hopper775/Analog_t12_controller/t12 iron/t12 iron.kicad_pcb

## KiCad design v0.0.1/cwbpf.kicad_pcb

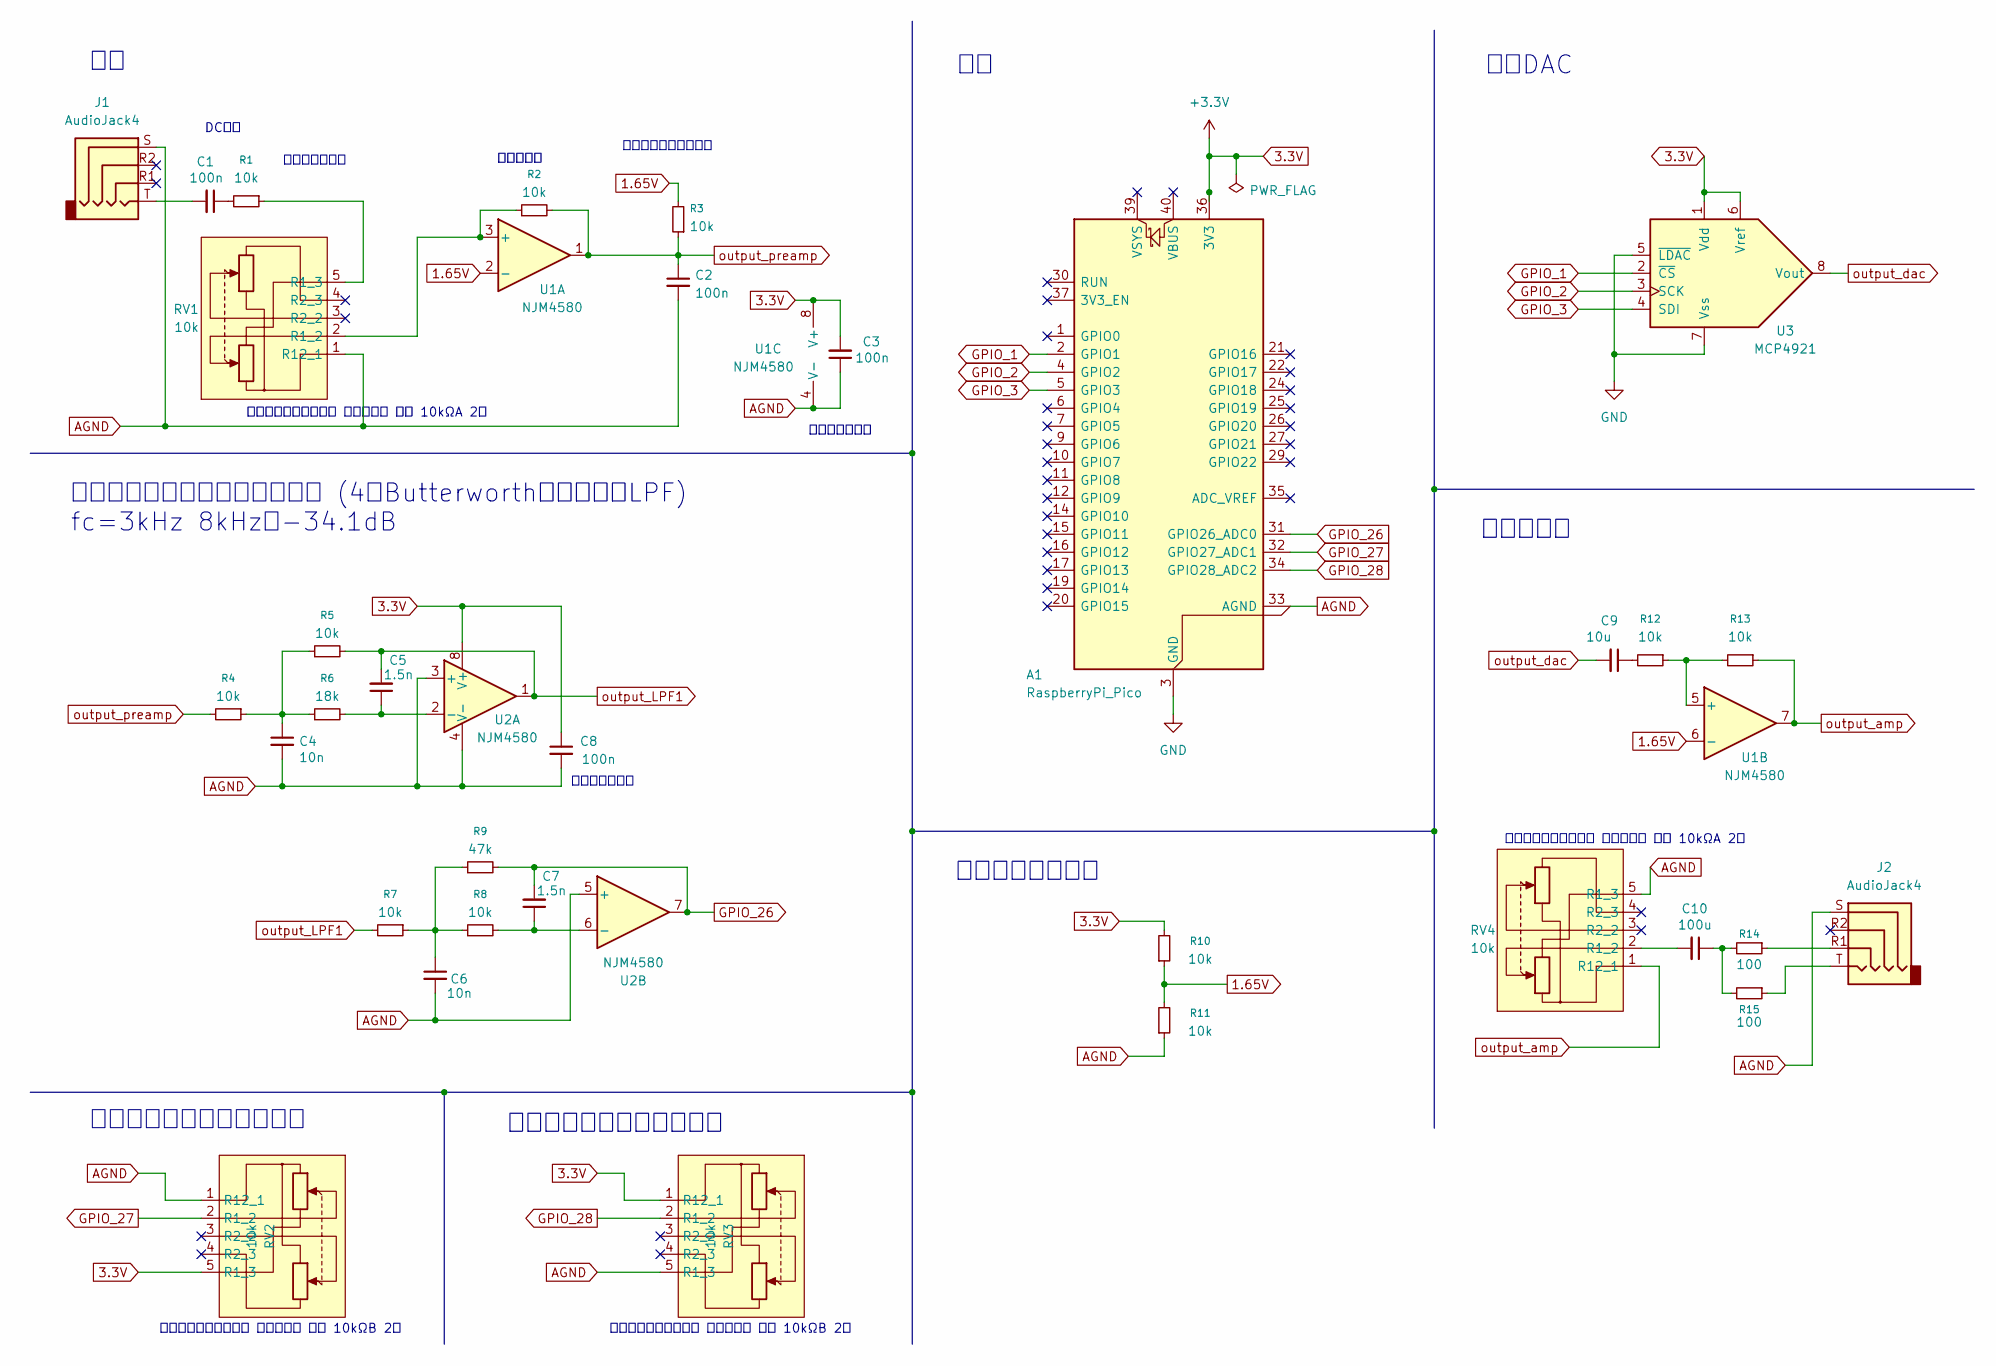
[picture p2: schematic cwbpf.kicad_sch]

Parts:
A1: RaspberryPi_Pico; RaspberryPi_Pico_slim
C1, C2, C3, C8: 100n; C_Disc_D7.5mm_W2.5mm_P5.00mm
C4, C6: 10n; C_Disc_D7.0mm_W2.5mm_P5.00mm
C5, C7: 1.5n; C_Disc_D7.0mm_W2.5mm_P5.00mm
C9: 10u; CP_Radial_D5.0mm_P2.00mm
C10: 100u; CP_Radial_D8.0mm_P3.50mm
J1, J2: AudioJack4; Jack_3.5mm_PJ320E_Horizontal
R1, R2, R3, R4, R5, R7, R8, R10, R11, R12, R13: 10k; R_Axial_DIN0204_L3.6mm_D1.6mm_P5.08mm_Horizontal
R6: 18k; R_Axial_DIN0204_L3.6mm_D1.6mm_P5.08mm_Horizontal
R9: 47k; R_Axial_DIN0204_L3.6mm_D1.6mm_P5.08mm_Horizontal
R14, R15: 100; R_Axial_DIN0204_L3.6mm_D1.6mm_P5.08mm_Horizontal
RV1, RV2, RV3, RV4: 10k; 基板取付用ボリューム つまみ付き 薄型 10kΩ 2連
U1, U2: NJM4580; SIP-8_19x3mm_P2.54mm
U3: MCP4921; DIP-8_W7.62mm

Connections:
1.65V: R3.2, R10.1, R11.2, U1.2 (-), U1.6 (-)
3.3V: A1.36 (3V3), C3.2, C8.1, R10.2, RV2.5 (R1_3), RV3.1 (R12_1), U1.8 (V+), U2.8 (V+), U3.1 (Vdd), U3.6 (Vref)
AGND: A1.33 (AGND), C2.2, C3.1, C4.2, C6.2, C8.2, J1.S, J2.S, R11.1, RV1.1 (R12_1), RV2.1 (R12_1), RV3.5 (R1_3), RV4.5 (R1_3), U1.4 (V-), U2.3 (+), U2.4 (V-), U2.5 (+)
GND: A1.3 (GND), A1.8 (GND), A1.13 (GND), A1.18 (GND), A1.23 (GND), A1.28 (GND), A1.38 (GND), U3.5 (~LDAC), U3.7 (Vss)
GPIO_1: A1.2 (GPIO1), U3.2 (~CS)
GPIO_2: A1.4 (GPIO2), U3.3 (SCK)
GPIO_3: A1.5 (GPIO3), U3.4 (SDI)
GPIO_26: A1.31 (GPIO26_ADC0), C7.2, R9.2, U2.7
GPIO_27: A1.32 (GPIO27_ADC1), RV2.2 (R1_2)
GPIO_28: A1.34 (GPIO28_ADC2), RV3.2 (R1_2)
unnamed: C1.1, R1.2
unnamed: C1.2, J1.T
unnamed: C4.1, R4.1, R5.1, R6.1
unnamed: C6.1, R7.1, R8.1, R9.1
unnamed: C9.1, R12.2
unnamed: C10.1, R14.2, R15.2
unnamed: J2.R1, R14.1
unnamed: J2.T, R15.1
unnamed: R2.1, RV1.2 (R1_2), U1.3 (+)
unnamed: R1.1, RV1.5 (R1_3)
unnamed: C10.2, RV4.2 (R1_2)
unnamed: R12.1, R13.2, U1.5 (+)
unnamed: C5.1, R6.2, U2.2 (-)
unnamed: C7.1, R8.2, U2.6 (-)
output_LPF1: C5.2, R5.2, R7.2, U2.1
output_amp: R13.1, RV4.1 (R12_1), U1.7
output_dac: C9.2, U3.8 (Vout)
output_preamp: C2.1, R2.2, R3.1, R4.2, U1.1

Notes on the sheet:
基板取付用ボリューム つまみ付き 薄型 10kΩB 2連
上限周波数調整ボリューム
下限周波数調整ボリューム
DC遮断
デカップリング
アンチエイリアシングフィルタ (4次Butterworth多重帰還型LPF) fc=3kHz 8kHzで-34.1dB
プリアンプ
バイアス電圧生成
基板取付用ボリューム つまみ付き 薄型 10kΩA 2連
出力アンプ
バイアス電圧重畳回路
入力ゲイン調整
出力DAC

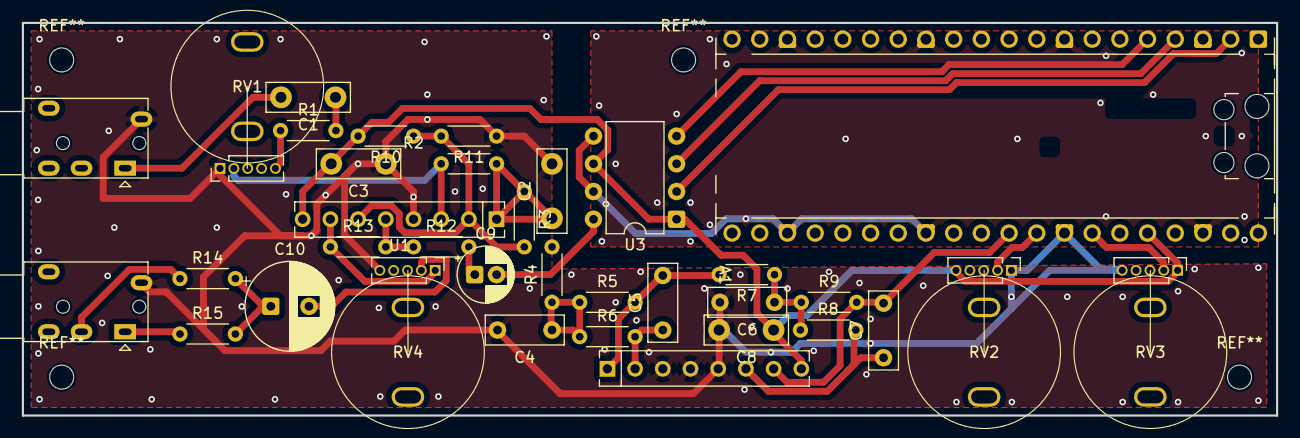
[picture p3: board cwbpf.kicad_pcb from above]

Board: 2 copper layers, 115.0 x 36.0 mm, 35 parts (0 on the bottom side), 28 nets.
